mpek29/HeaterControl-Shield/technological_choice/wheastone_bridge_accompaniment/wheastone_bridge_accompaniment_001.pdf

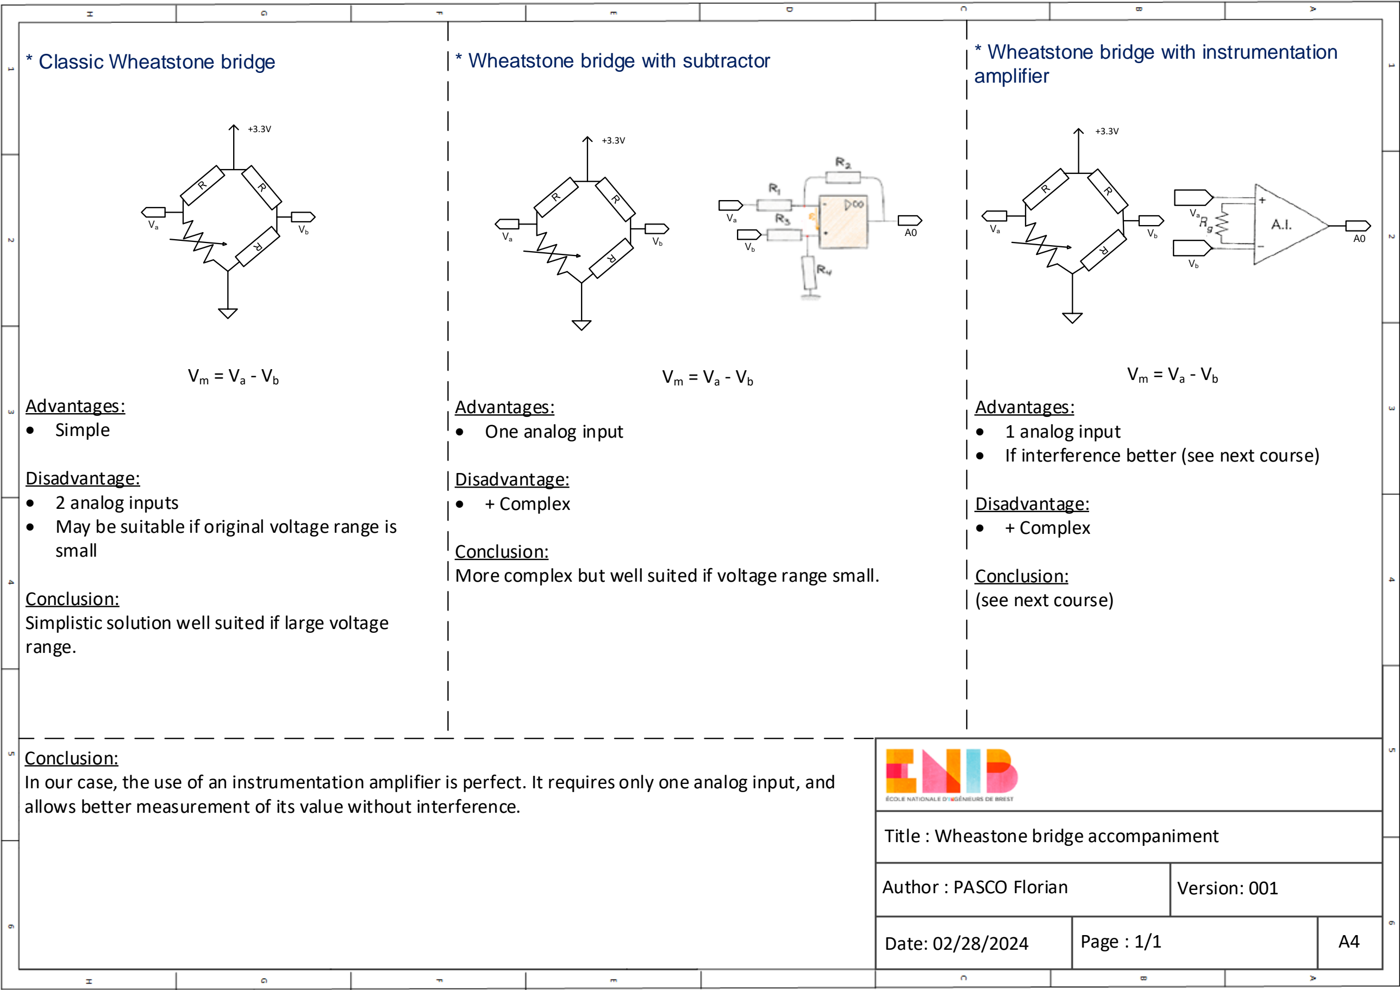
[picture p11: page 1]

Title : Wheastone bridge accompaniment

Author : PASCO Florian | Version: 001
Date: 02/28/2024 | Page : 1/1 | A4
* Classic Wheatstone bridge | * Wheatstone bridge with subtractor | * Wheatstone bridge with instrumentation amplifier

Vm = Va - Vb
Advantages:
- Simple

Disadvantage:
- 2 analog inputs
- May be suitable if original voltage range is small

Conclusion:
Simplistic solution well suited if large voltage range.

Advantages:
- One analog input

Disadvantage:
- + Complex

Conclusion:
More complex but well suited if voltage range small.

Advantages:
- 1 analog input
- If interference better (see next course)

Disadvantage:
- + Complex

Conclusion:
(see next course)

Conclusion:
In our case, the use of an instrumentation amplifier is perfect. It requires only one analog input, and allows better measurement of its value without interference.
Vm = Va - Vb | Vm = Va - Vb

Vb

Va

A0

+3.3V

Va | Vb | A0

Vb

Va

+3.3V

Va | Vb

+3.3V

Va | Vb
