mpek29/HeaterControl-Shield/sim/mosfet_sim.asc

M1: nmos; SP8M24_N
R1: res; 10k
V1: voltage; 24
V2: voltage; PULSE(0 5 5m 0.01m 0.01m 5m 10m)
Named nets: 0, Ve, CMD_ther, 24V
.tran 100m
