mpek29/HeaterControl-Shield/sim/tension_divider.asc

R1: res; 1k
R2: res; 10k
R3: res; 1k
R4: res; 10k
R5: res; 2k
V1: voltage; 24
V2: voltage; 24
Named nets: 0, Vs1, Vs2
.tran 10
